habworks/TechnologyDemonstrator/Documents/Block Diagram2.png

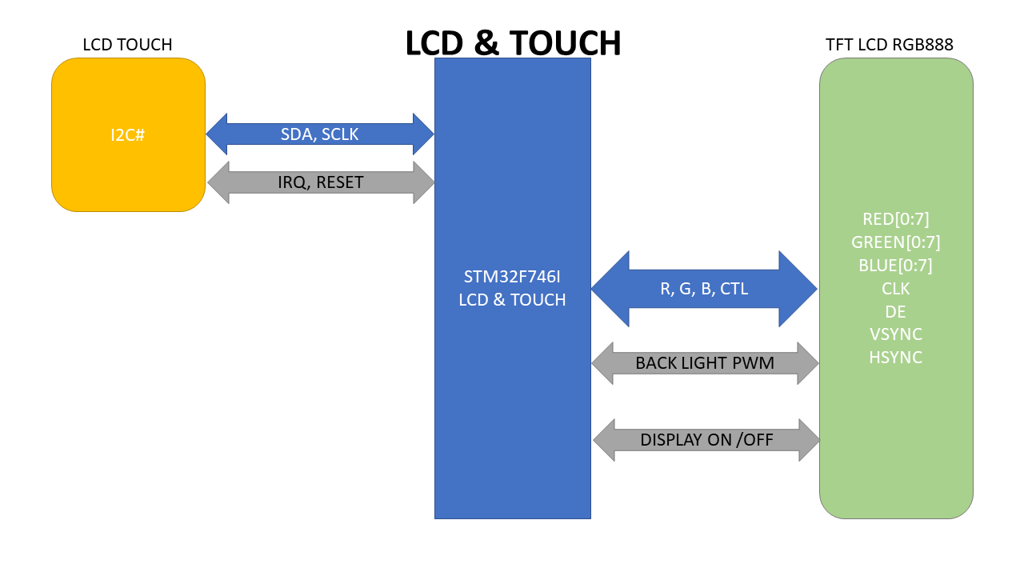
Documents/Block Diagram2.png
