habworks/TechnologyDemonstrator/Documents/Block Diagram 1.png

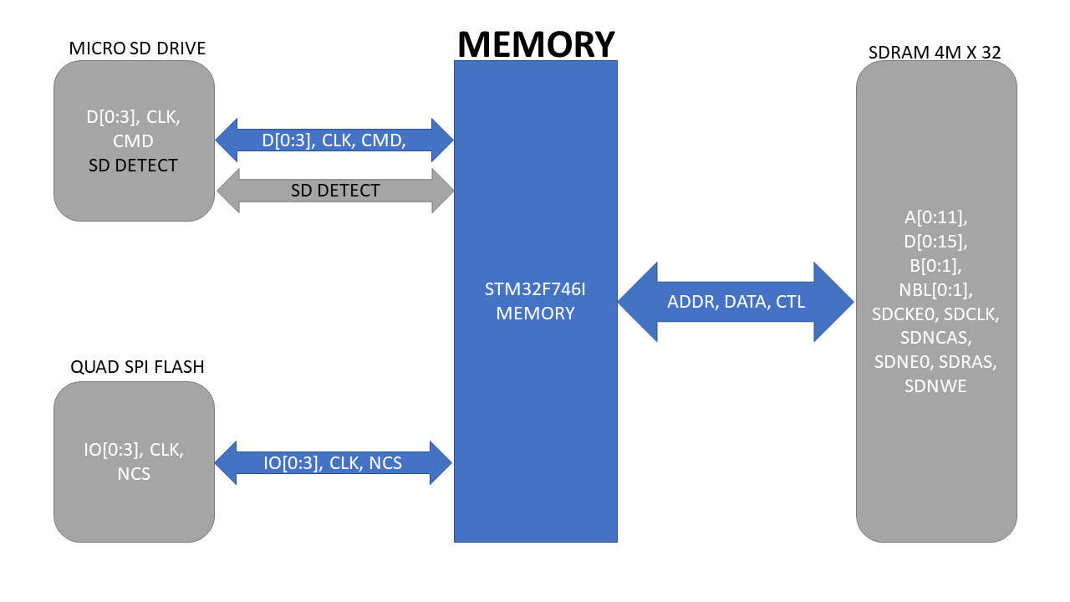
Documents/Block Diagram 1.png
