habworks/TechnologyDemonstrator/Documents/Block Diagram 5.png

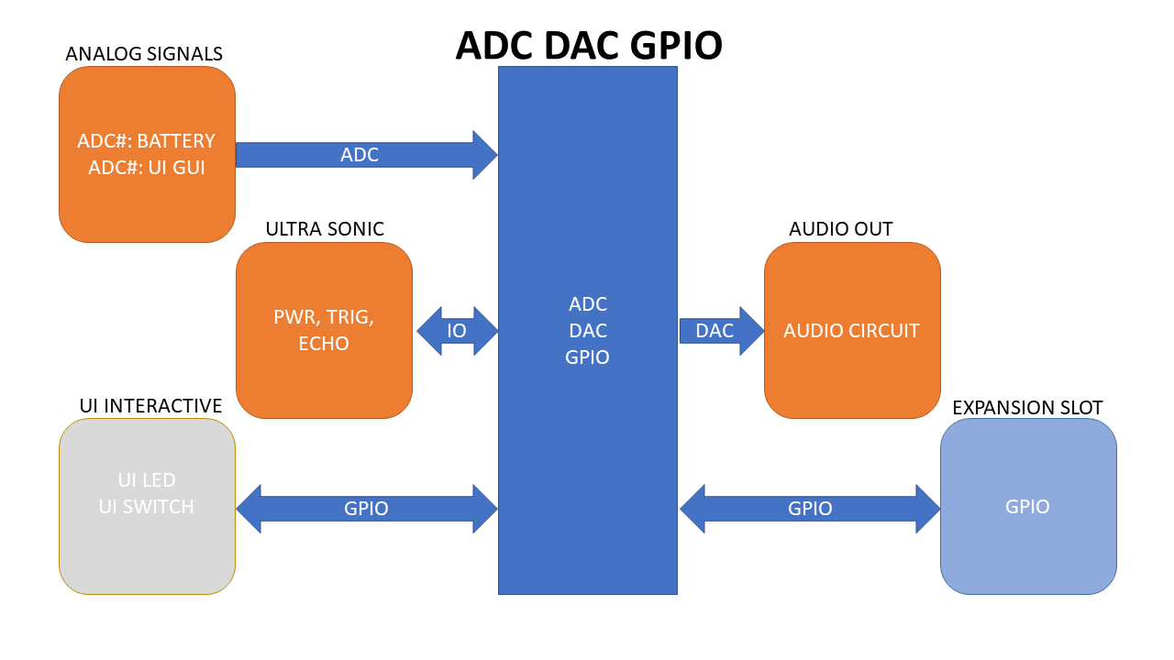
Documents/Block Diagram 5.png
