habworks/TechnologyDemonstrator/Hardware/3D_Models/RES_0805.step

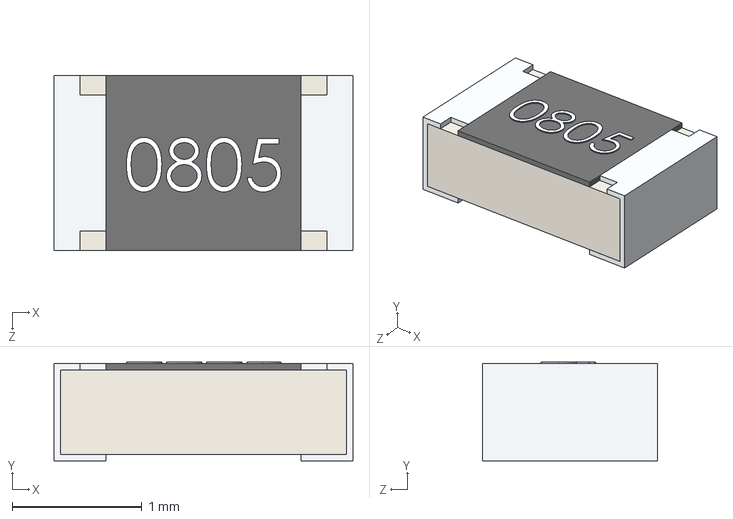
[picture p25: CAD file, 2020-11-24]
Hardware/3D_Models/RES_0805.step
2.30 x 0.76 x 1.35 mm
