habworks/TechnologyDemonstrator/Hardware/3D_Models/SOT-23.STEP

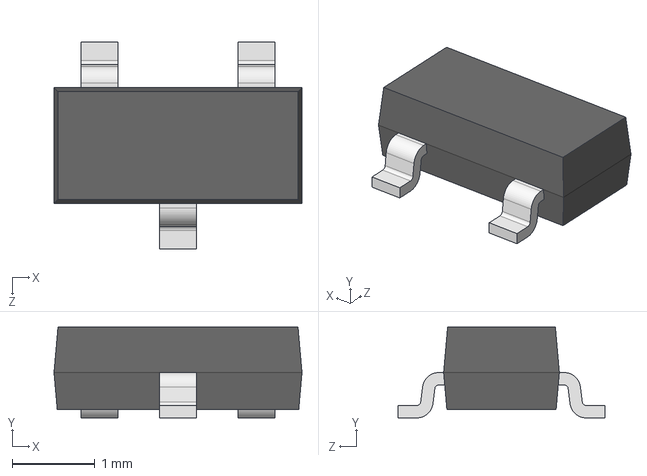
[picture p26: CAD file, 2020-11-24]
Hardware/3D_Models/SOT-23.STEP
3.00 x 1.10 x 2.50 mm
