habworks/TechnologyDemonstrator/Hardware/3D_Models/COILCRAFT_LPS4018.step

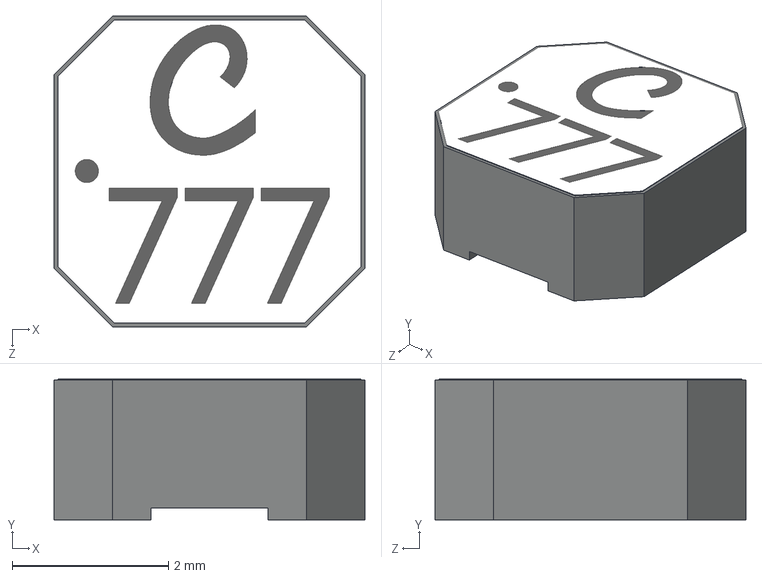
[picture p27: CAD file, 2020-11-24]
Hardware/3D_Models/COILCRAFT_LPS4018.step
3.98 x 1.80 x 3.98 mm
