habworks/TechnologyDemonstrator/Hardware/3D_Models/1206.step

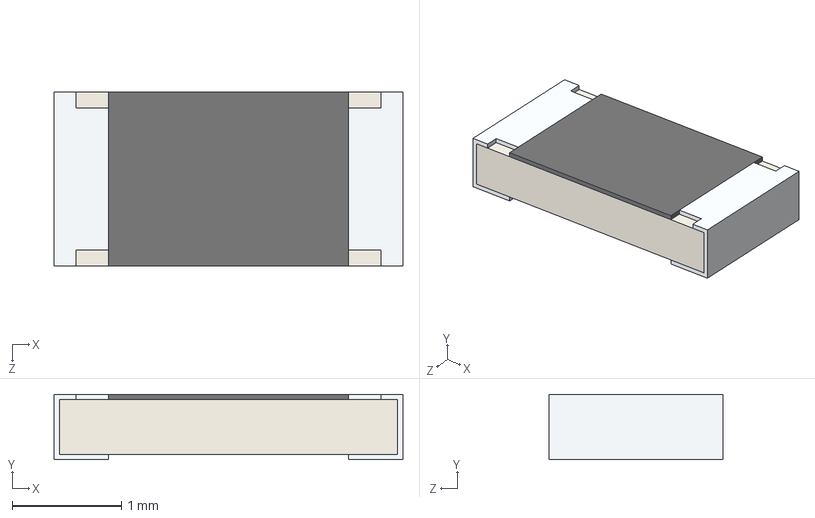
[picture p28: CAD file, 2020-11-24]
Hardware/3D_Models/1206.step
3.20 x 0.6 x 1.60 mm
