habworks/TechnologyDemonstrator/Hardware/3D_Models/CONN_HDR_1X3_100MIL.stp

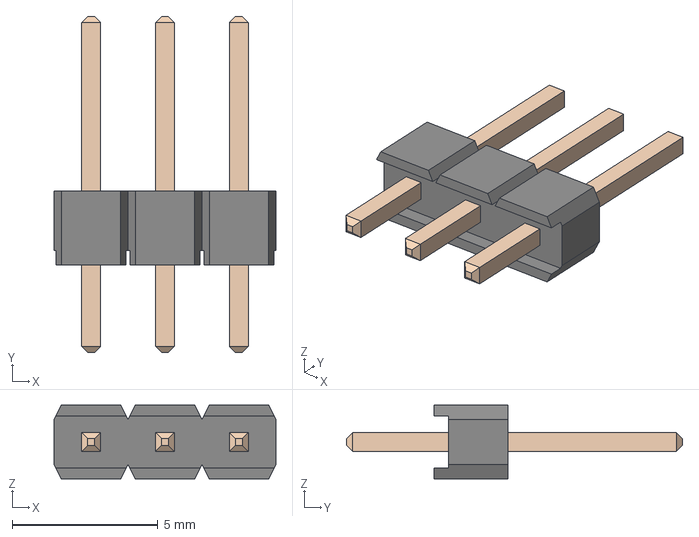
[picture p29: CAD file, 2020-11-24]
Hardware/3D_Models/CONN_HDR_1X3_100MIL.stp
7.62 x 11.5 x 2.54 mm
