habworks/TechnologyDemonstrator/Hardware/3D_Models/ECX-32.STEP

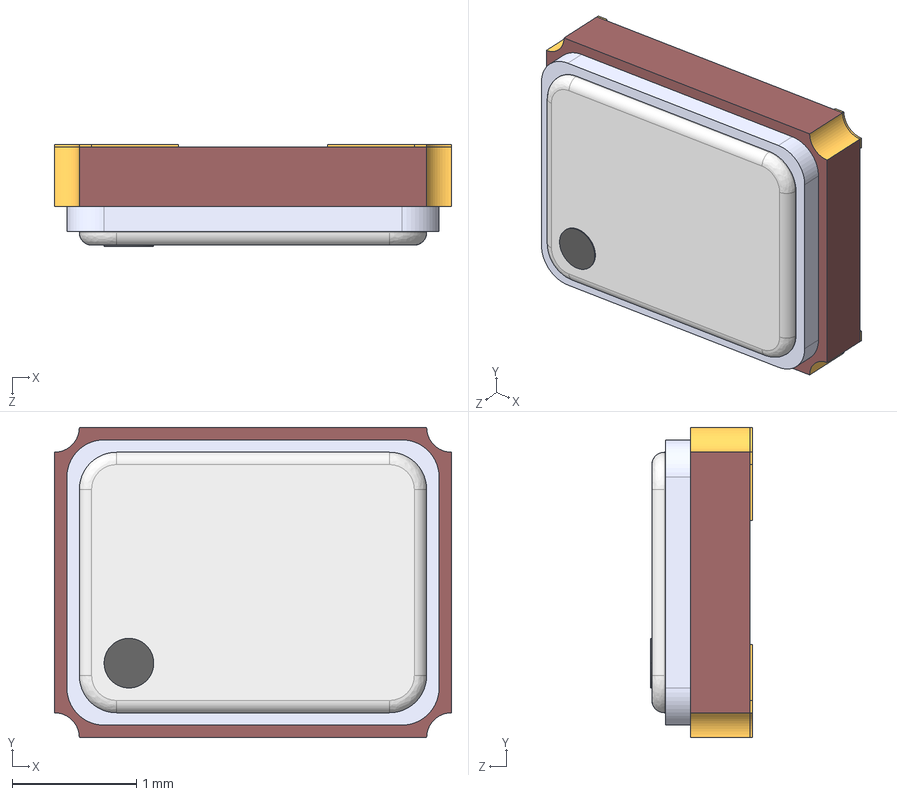
[picture p30: CAD file, 2020-11-24]
Hardware/3D_Models/ECX-32.STEP
3.20 x 2.50 x 0.82 mm
MetalFrame
Pin1Marker
Pin3
Pin1
Lid
Pin4
Pin2
Ceramic
