habworks/TechnologyDemonstrator/Hardware/3D_Models/SMB.step

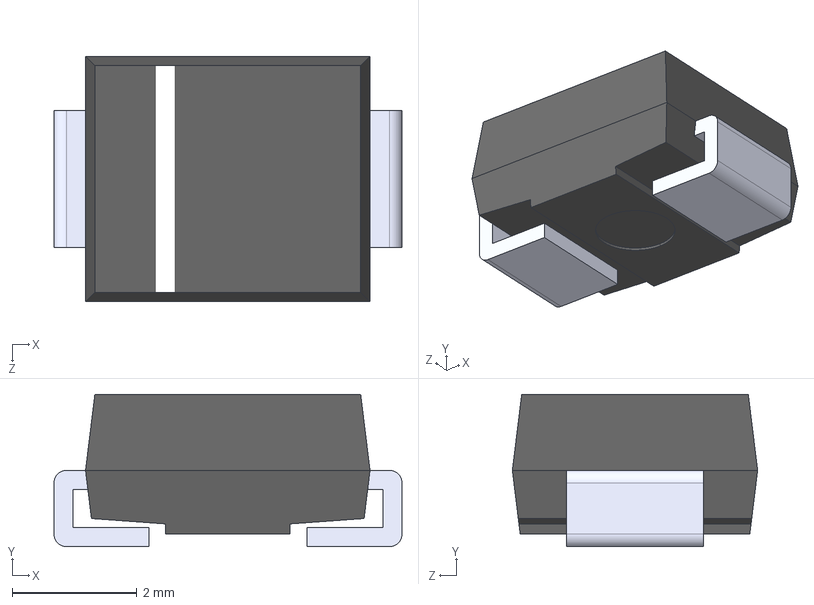
[picture p31: CAD file, 2020-11-24]
Hardware/3D_Models/SMB.step
5.59 x 2.45 x 3.94 mm
