habworks/TechnologyDemonstrator/Hardware/3D_Models/14VSON.step

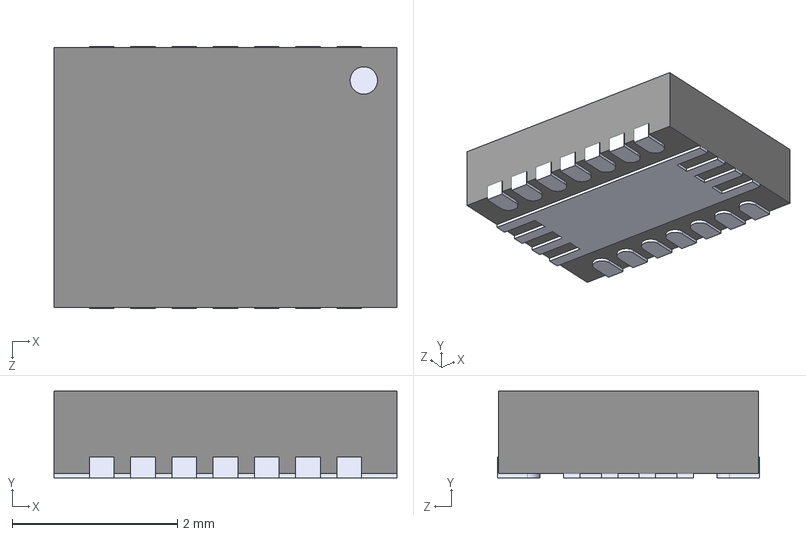
[picture p32: CAD file, 2020-11-24]
Hardware/3D_Models/14VSON.step
4.15 x 1.05 x 3.17 mm
