habworks/TechnologyDemonstrator/Hardware/3D_Models/SOIC8_WIDE.step

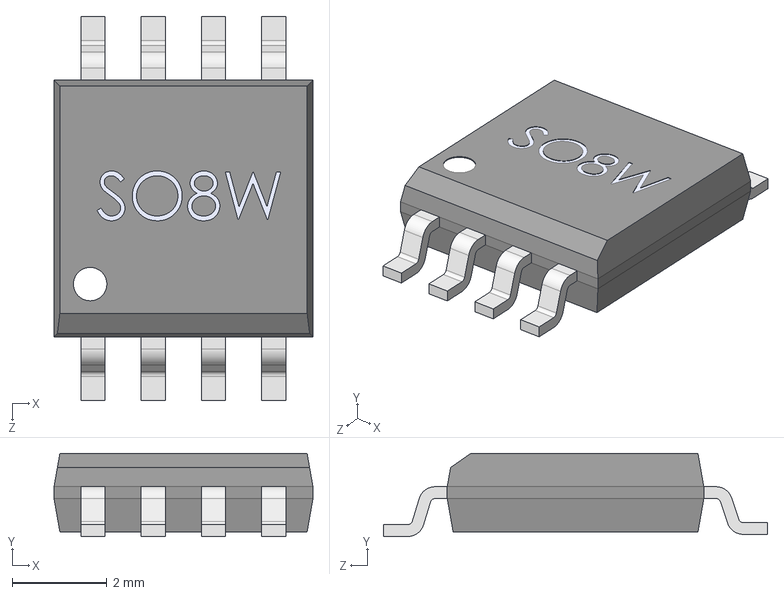
[picture p33: CAD file, 2020-11-24]
Hardware/3D_Models/SOIC8_WIDE.step
5.46 x 1.75 x 8.10 mm
