habworks/TechnologyDemonstrator/Hardware/3D_Models/ST_LIS3DHTR.step

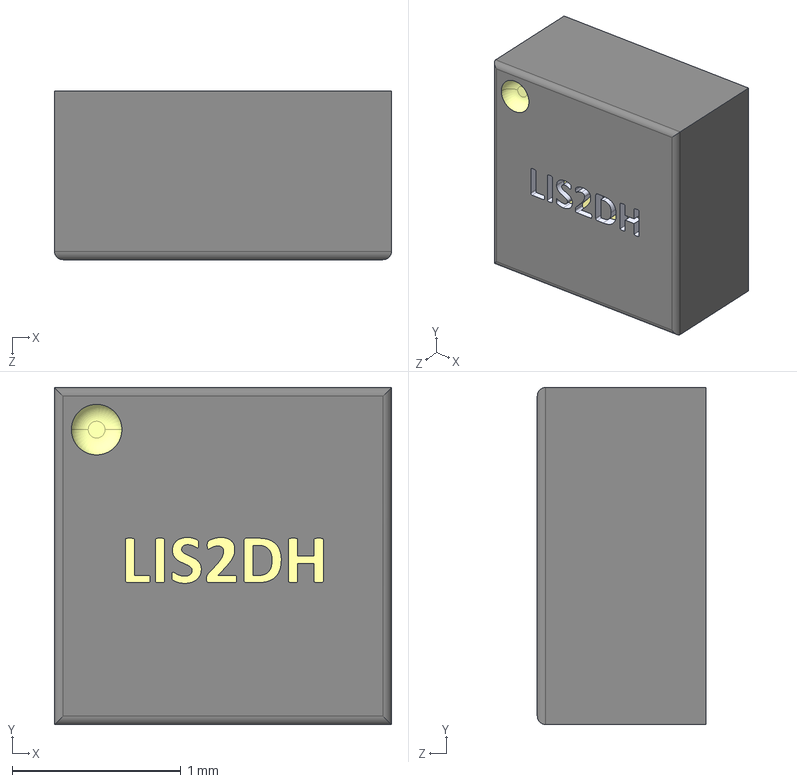
[picture p34: CAD file, 2020-11-24]
Hardware/3D_Models/ST_LIS3DHTR.step
2.00 x 2.00 x 1.00 mm
