habworks/TechnologyDemonstrator/Hardware/3D_Models/CONN_HDR_1X2_100MIL.stp

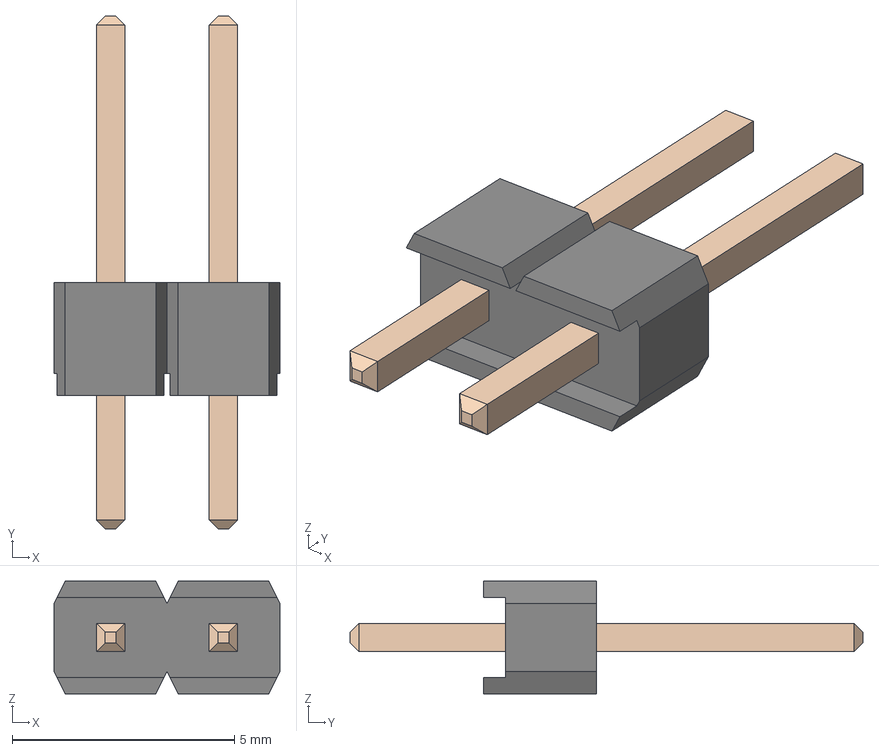
[picture p35: CAD file, 2020-11-24]
Hardware/3D_Models/CONN_HDR_1X2_100MIL.stp
5.08 x 11.5 x 2.54 mm
