habworks/TechnologyDemonstrator/Hardware/3D_Models/CONN_HDR_1X6_100MIL.stp

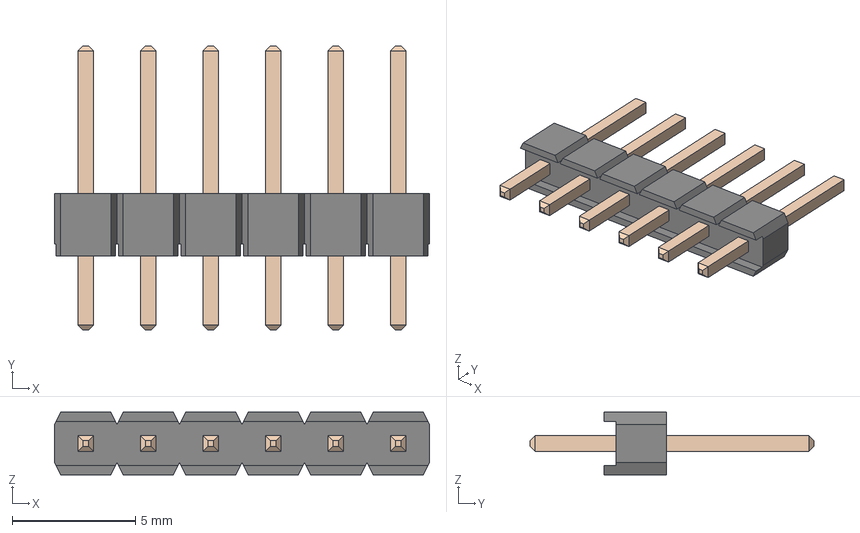
[picture p36: CAD file, 2020-11-24]
Hardware/3D_Models/CONN_HDR_1X6_100MIL.stp
15.2 x 11.5 x 2.54 mm
