habworks/TechnologyDemonstrator/Hardware/3D_Models/CONN_MOLEX_541044033.stp

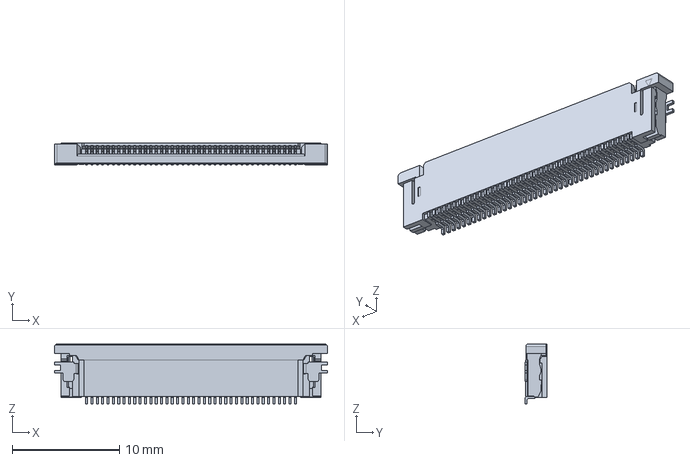
[picture p37: CAD file, 2020-11-24]
Hardware/3D_Models/CONN_MOLEX_541044033.stp
25.5 x 2.05 x 5.60 mm
