habworks/TechnologyDemonstrator/Hardware/3D_Models/User Library-EVQ-P2-H02B_K02Q+3P202K.step

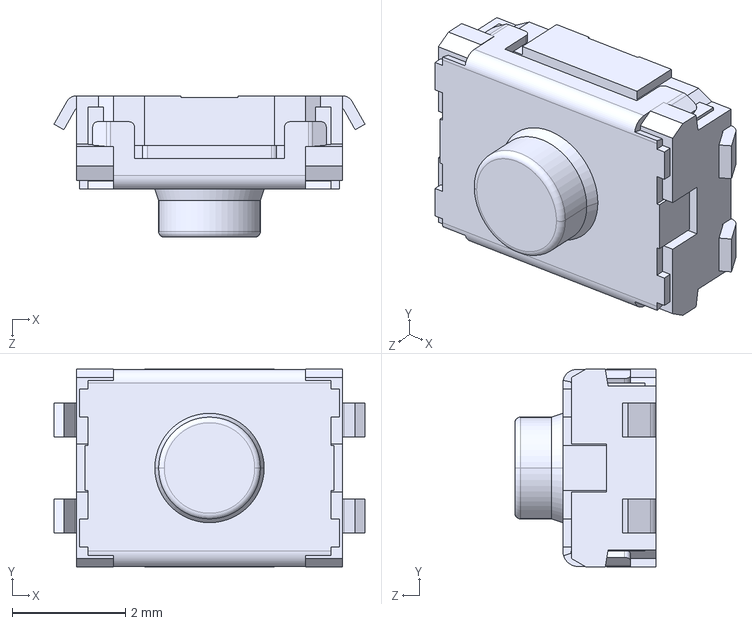
[picture p38: CAD file, 2020-11-24]
Hardware/3D_Models/User Library-EVQ-P2-H02B_K02Q+3P202K.step
5.50 x 3.50 x 2.50 mm
