habworks/TechnologyDemonstrator/Hardware/3D_Models/CONN_HDR_SOCKET_1X5_100MIL.step

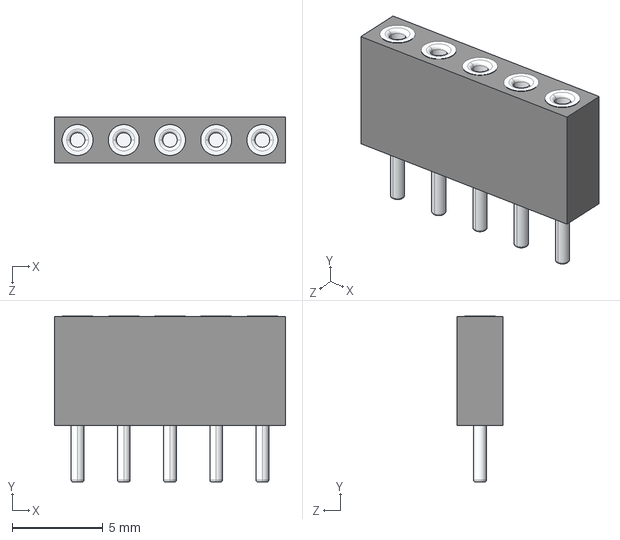
[picture p39: CAD file, 2020-11-24]
Hardware/3D_Models/CONN_HDR_SOCKET_1X5_100MIL.step
12.7 x 9.12 x 2.54 mm
