habworks/TechnologyDemonstrator/Hardware/3D_Models/WRL-17146.step

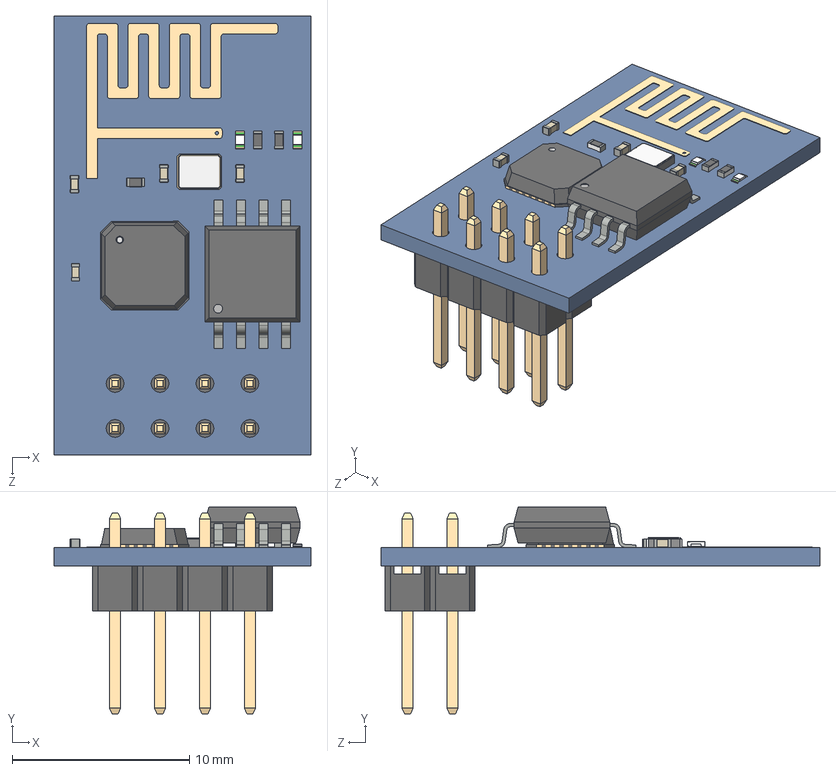
[picture p40: CAD file, 2020-11-24]
Hardware/3D_Models/WRL-17146.step
14.5 x 11.7 x 24.8 mm
