habworks/TechnologyDemonstrator/Hardware/3D_Models/IND_SDR0403.step

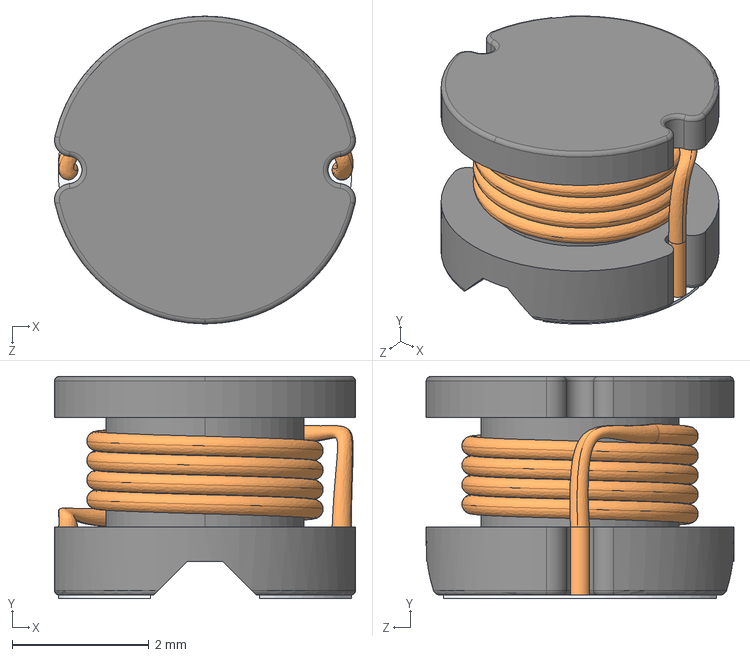
[picture p41: CAD file, 2020-11-24]
Hardware/3D_Models/IND_SDR0403.step
4.40 x 3.25 x 4.50 mm
