habworks/TechnologyDemonstrator/Hardware/3D_Models/4PLCC-LED.step

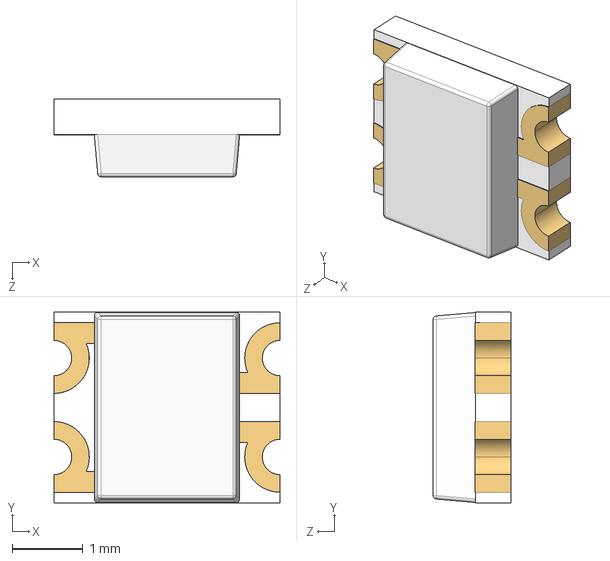
[picture p42: CAD file, 2020-11-24]
Hardware/3D_Models/4PLCC-LED.step
3.20 x 2.70 x 1.10 mm
