habworks/TechnologyDemonstrator/Hardware/3D_Models/SOT363-6.step

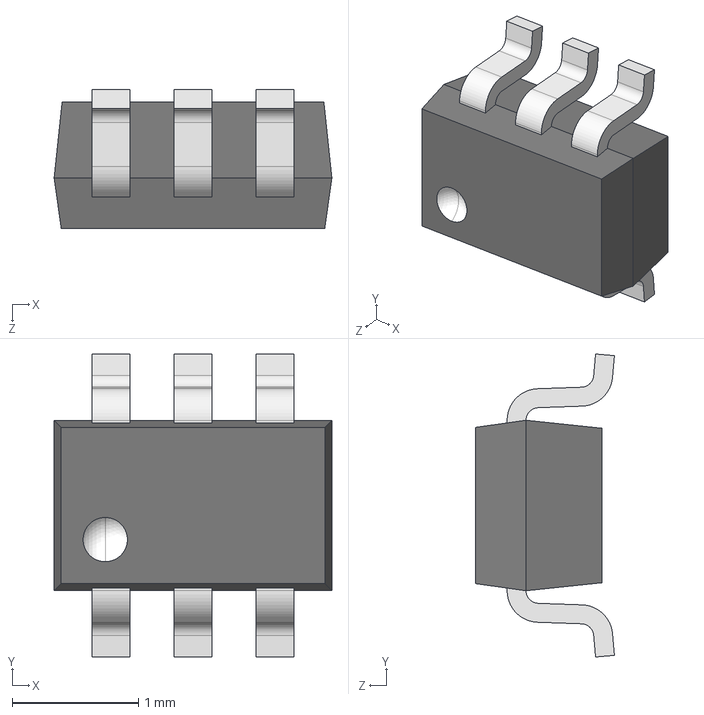
[picture p43: CAD file, 2020-11-24]
Hardware/3D_Models/SOT363-6.step
2.20 x 2.40 x 1.10 mm
