habworks/TechnologyDemonstrator/Hardware/3D_Models/CONN_MOLEX_522710679.stp

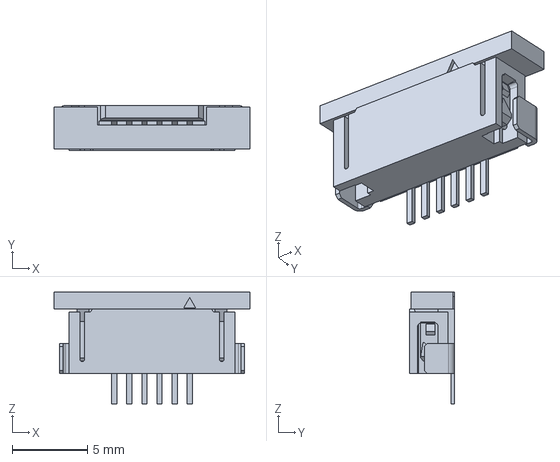
[picture p44: CAD file, 2020-11-24]
Hardware/3D_Models/CONN_MOLEX_522710679.stp
13.0 x 3.00 x 7.40 mm
