habworks/TechnologyDemonstrator/Hardware/3D_Models/SOD123.STEP

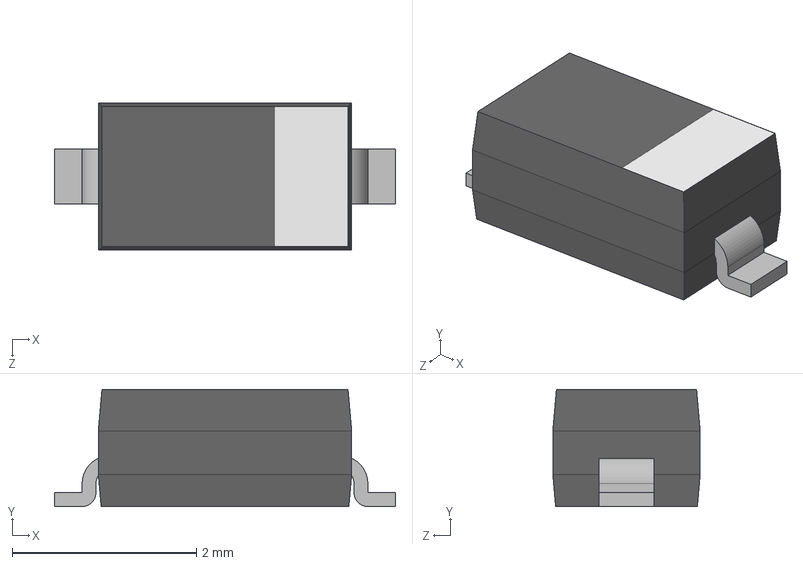
[picture p45: CAD file, 2020-11-24]
Hardware/3D_Models/SOD123.STEP
3.70 x 1.27 x 1.60 mm
