habworks/TechnologyDemonstrator/Hardware/3D_Models/RES_0603.STEP

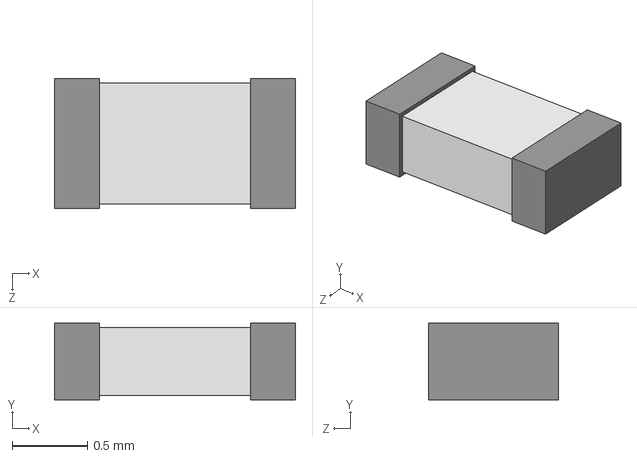
[picture p46: CAD file, 2020-11-24]
Hardware/3D_Models/RES_0603.STEP
1.60 x 0.51 x 0.86 mm
