habworks/TechnologyDemonstrator/Hardware/3D_Models/SOD323.STEP

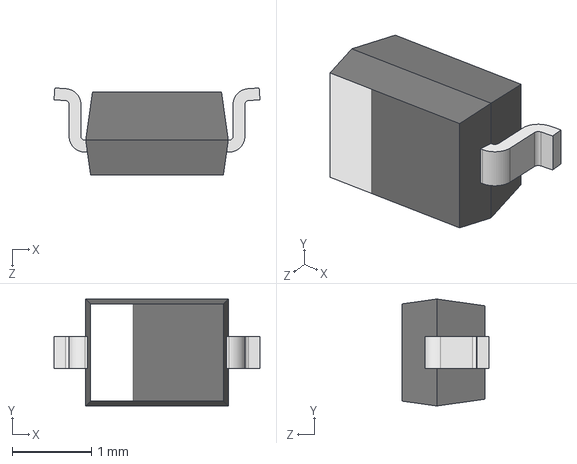
[picture p47: CAD file, 2020-11-24]
Hardware/3D_Models/SOD323.STEP
2.60 x 1.35 x 1.10 mm
