habworks/TechnologyDemonstrator/Hardware/3D_Models/ECS-250-18-7SX-TR.STEP

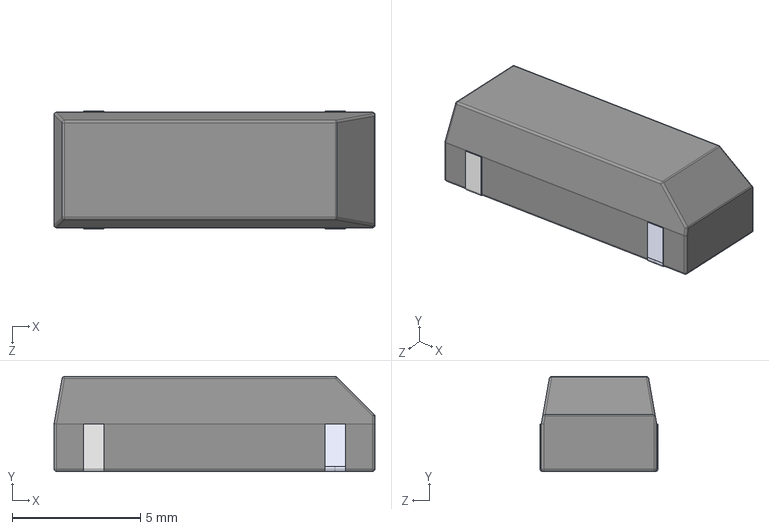
[picture p48: CAD file, 2020-11-24]
Hardware/3D_Models/ECS-250-18-7SX-TR.STEP
12.5 x 3.70 x 4.60 mm
