habworks/TechnologyDemonstrator/Hardware/3D_Models/CAP_ALE_SMD_6.6x6.6.STEP

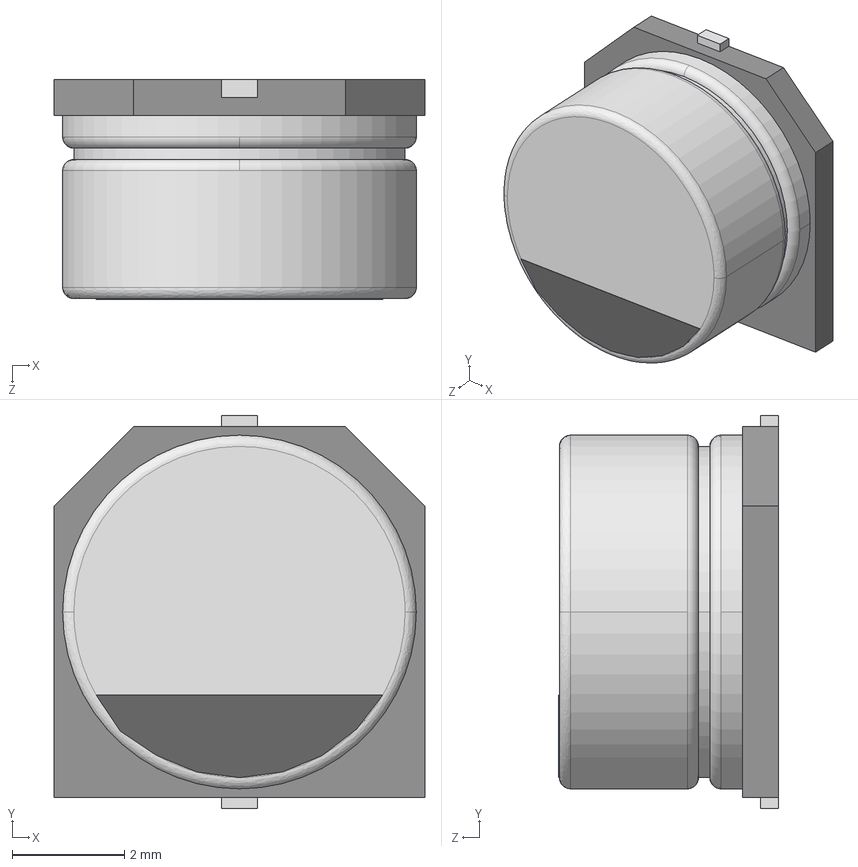
[picture p49: CAD file, 2020-11-24]
Hardware/3D_Models/CAP_ALE_SMD_6.6x6.6.STEP
6.60 x 7.00 x 3.91 mm
CAP003
CAP
CAP001
CAP002
CAP004
