habworks/TechnologyDemonstrator/Hardware/3D_Models/SOIC8.step

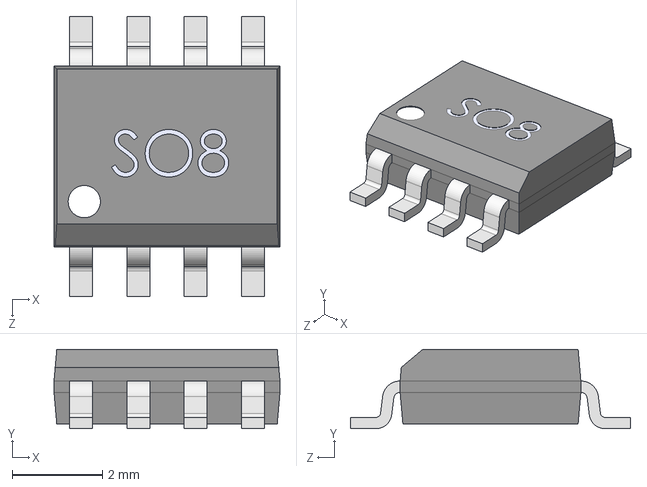
[picture p50: CAD file, 2020-11-24]
Hardware/3D_Models/SOIC8.step
5.00 x 1.75 x 6.20 mm
