habworks/TechnologyDemonstrator/Hardware/3D_Models/SC70-5_SOT-353_5-TSSOP.STEP

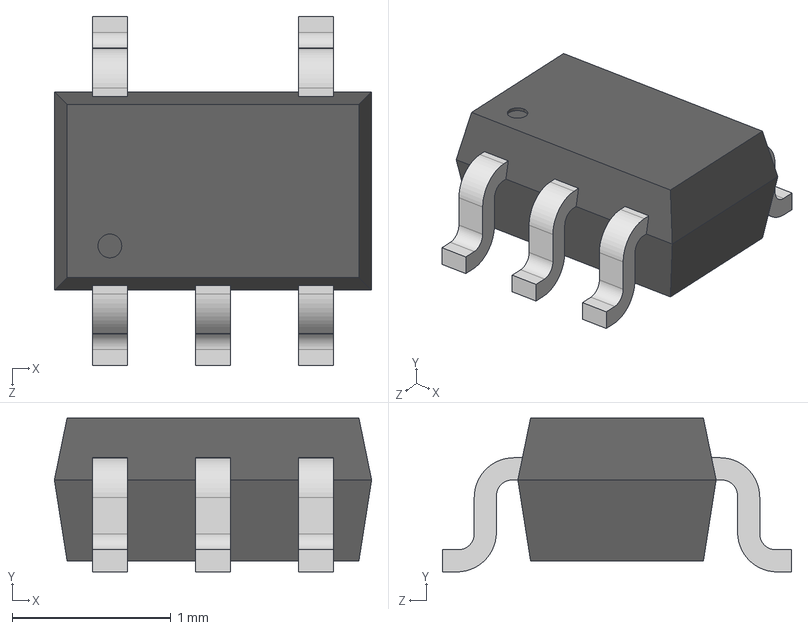
[picture p51: CAD file, 2020-11-24]
Hardware/3D_Models/SC70-5_SOT-353_5-TSSOP.STEP
2.00 x 0.97 x 2.20 mm
