habworks/TechnologyDemonstrator/AppFirmware/TD_AppFirmware/Core/App_Src/QuadSPI_Support.c

/** ****************************************************************************************************
 * @file 			MainSupport.c
 * @brief			This is the Source file used to support the quadspic.c CubeMx generated file
 * ****************************************************************************************************
 * @author			Hab S. Collector \n
 * Last Edited By:	Hab S. Collector \n
 *
 * @date			3/7/21 \n
 * @version       	See Main_Support.h: FIRMWARE_REV_MAJOR, FIRMWARE_REV_MINOR
 *
 * @param Development_Environment \n
 * Hardware:		STM32F746IGT6 \n
 * IDE:             STM32CubeIDE, VER 1.5.1 \n
 * Compiler:        GCC \n
 * Editor Settings: 1 Tab = 4 Spaces, Recommended Courier New 11
 *
 * @note            This file provides a function that supports the QUAD SPI init function (MX_QUADSPI_Init())
 * 					I did not write this code, but rather is was copied from a working sample project
 * 					The function here in should be inserted as the last line of the function
 * 					EVERYTIME THE .IOC file regenerates it will remove that last line - you must reinsert
 *
 *
 * 					This is an embedded application
 *		            It will be necessary to consult the reference documents to fully understand the code
 *                  It is suggested that the documents be reviewed in the order shown.
 *			          IMR Technology Demonstrator Schematic: IMR002S REV 1
 *				      IMR Technology Demonstrator Schematic: IMR002S REV 1
 *
 * @copyright		IMR Engineering
 * **************************************************************************************************** */

#include "QuadSPI_Support.h"
#include "stm32746g_discovery_qspi.h"


void quadSPI_InitSupport(void)
{

	// QUAD SPI INIT CODE
	BSP_QSPI_Init();
	BSP_QSPI_MemoryMappedMode();
	HAL_NVIC_DisableIRQ(QUADSPI_IRQn);

	// MPU SUPPORT
	MPU_Region_InitTypeDef MPU_InitStruct = {0};
	/* Disables the MPU */
	HAL_MPU_Disable();
	/** Initializes and configures the Region and the memory to be protected
	*/
	MPU_InitStruct.Enable = MPU_REGION_ENABLE;
	MPU_InitStruct.Number = MPU_REGION_NUMBER0;
	MPU_InitStruct.BaseAddress = 0x90000000;
	MPU_InitStruct.Size = MPU_REGION_SIZE_256MB;
	MPU_InitStruct.SubRegionDisable = 0x0;
	MPU_InitStruct.TypeExtField = MPU_TEX_LEVEL0;
	MPU_InitStruct.AccessPermission = MPU_REGION_FULL_ACCESS;
	MPU_InitStruct.DisableExec = MPU_INSTRUCTION_ACCESS_ENABLE;
	MPU_InitStruct.IsShareable = MPU_ACCESS_NOT_SHAREABLE;
	MPU_InitStruct.IsCacheable = MPU_ACCESS_NOT_CACHEABLE;
	MPU_InitStruct.IsBufferable = MPU_ACCESS_NOT_BUFFERABLE;

	HAL_MPU_ConfigRegion(&MPU_InitStruct);
	/** Initializes and configures the Region and the memory to be protected
	*/
	MPU_InitStruct.Enable = MPU_REGION_ENABLE;
	MPU_InitStruct.Number = MPU_REGION_NUMBER1;
	MPU_InitStruct.BaseAddress = 0x90000000;
	MPU_InitStruct.Size = MPU_REGION_SIZE_16MB;
	MPU_InitStruct.SubRegionDisable = 0x0;
	MPU_InitStruct.TypeExtField = MPU_TEX_LEVEL0;
	MPU_InitStruct.AccessPermission = MPU_REGION_FULL_ACCESS;
	MPU_InitStruct.DisableExec = MPU_INSTRUCTION_ACCESS_ENABLE;
	MPU_InitStruct.IsShareable = MPU_ACCESS_NOT_SHAREABLE;
	MPU_InitStruct.IsCacheable = MPU_ACCESS_CACHEABLE;
	MPU_InitStruct.IsBufferable = MPU_ACCESS_NOT_BUFFERABLE;

	HAL_MPU_ConfigRegion(&MPU_InitStruct);
	/* Enables the MPU */
	HAL_MPU_Enable(MPU_PRIVILEGED_DEFAULT);
}
