habworks/TechnologyDemonstrator/Firmware/TestHardware/Core/Inc/TimerSupport.h

/*
 * Time.h
 *
 *  Created on: Jan 16, 2021
 *      Author: IMR HabPC
 */

#ifndef INC_TIME_H_
#define INC_TIME_H_

#include "MainSupport.h"

// FUNCTION PROTOTYPES
void delayMiliSecond(uint32_t DelayTime);


#endif /* INC_TIME_H_ */
