habworks/TechnologyDemonstrator/Firmware/TestHardware/Core/Src/TimerSupport.c

/*
 * Timer.c
 *
 *  Created on: Jan 15, 2021
 *      Author: IMR HabPC
 */

#include "TimerSupport.h"


/* This function is the part of the Sys Tick timer.  It is defined weak else where.
 * FOR SYSTEM TIMER TO WORK YOU MUST INCLUDE ITS BASIC DUTIES AND INCLUDE:
 *    uwTick += uwTickFreq;
 * HAL_Delay() will need this
 */
void HAL_IncTick(void)
{
	uwTick += uwTickFreq;
	BoardStatus.GreenLedMsCounter++;
	BoardStatus.RedLedMsCounter++;
	BoardStatus.StatusLedMsCounter++;
	BoardStatus.MiliSecondCounter++;
}

void delayMiliSecond(uint32_t DelayTime)
{
	BoardStatus.MiliSecondCounter = 0;
	while (BoardStatus.MiliSecondCounter < DelayTime);
}
